emeb/up5k_osc/gateware/riscv/c/acia.h

/*
 * acia.h - serial port driver
 * 07-01-19 E. Brombaugh
 */

#ifndef __acia__
#define __acia__

#include "up5k_osc.h"

void acia_putc(char c);
void acia_printf_putc(void* p, char c);
void acia_puts(char *str);
int acia_getc(void);

#endif
